sudoroom/magnets/fuck-surveillance/surveillance.dxf

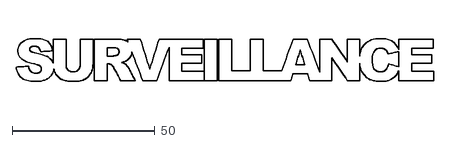
[picture p15: CAD file, 2014-02-05]
fuck-surveillance/surveillance.dxf
146.3 x 15.1
