sudoroom/magnets/hack-the-planet/mesh.stl

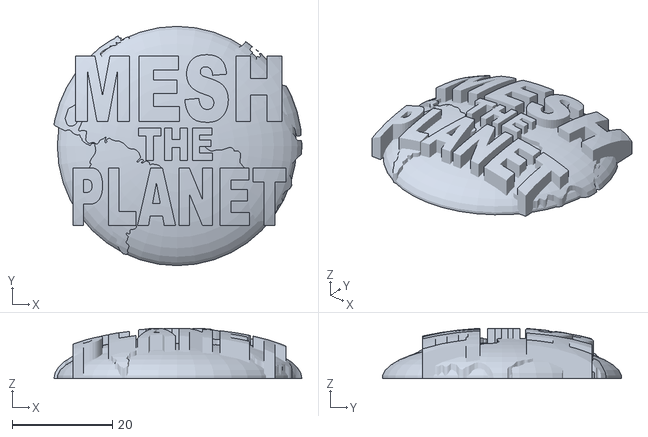
[picture p16: CAD file, 2014-01-22]
hack-the-planet/mesh.stl
49.6 x 47.9 x 10.0
