sudoroom/magnets/sudo/shrunk.dxf

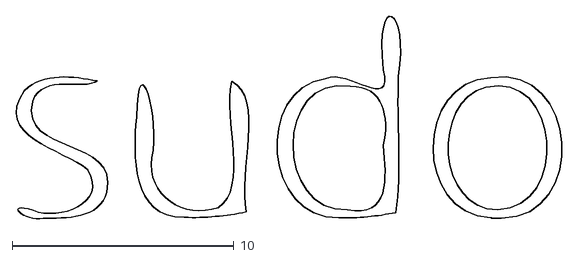
[picture p17: CAD file, 2014-01-15]
sudo/shrunk.dxf
24.6 x 9.11
