sudoroom/magnets/fuck-surveillance/fuck.dxf

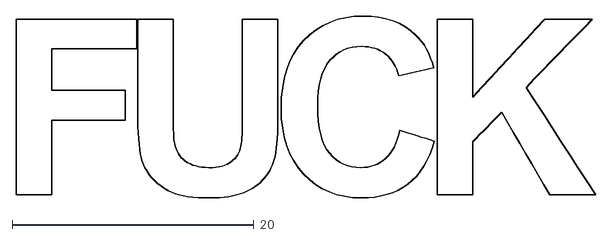
[picture p18: CAD file, 2014-02-05]
fuck-surveillance/fuck.dxf
47.9 x 15.0
