sudoroom/magnets/hack-the-planet/mesh_the_planet.dxf

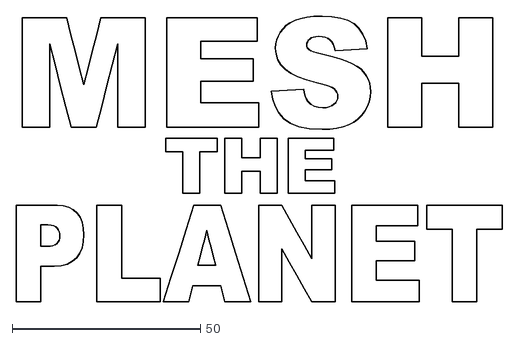
[picture p19: CAD file, 2014-01-13]
hack-the-planet/mesh_the_planet.dxf
129.1 x 75.9
