sudoroom/magnets/fuck-surveillance/no.dxf

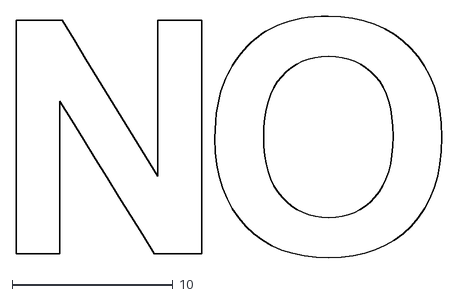
[picture p20: CAD file, 2014-02-05]
fuck-surveillance/no.dxf
26.5 x 15.0
