sudoroom/magnets/hack-the-planet/hack_the_planet.dxf

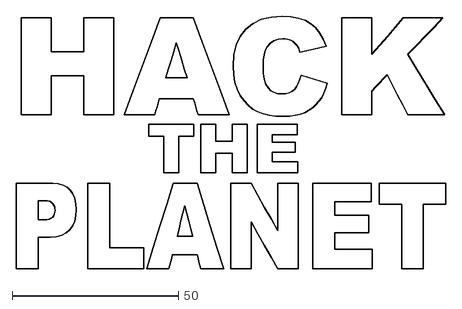
[picture p21: CAD file, 2014-01-12]
hack-the-planet/hack_the_planet.dxf
129.1 x 75.9
