sudoroom/magnets/fuck-surveillance/pictures.dxf

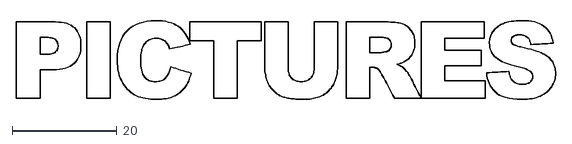
[picture p22: CAD file, 2014-02-05]
fuck-surveillance/pictures.dxf
103.0 x 15.1
