sudoroom/magnets/hack-the-planet/americas.dxf

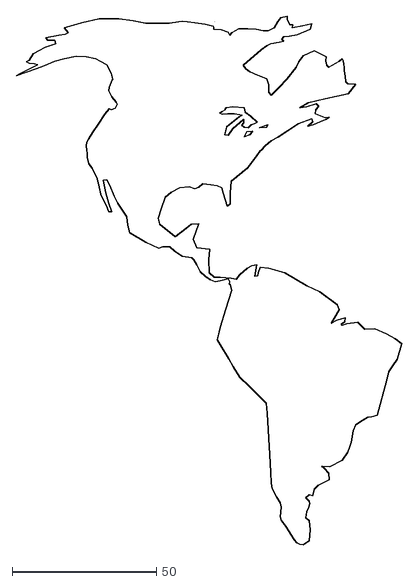
[picture p23: CAD file, 2014-01-11]
hack-the-planet/americas.dxf
133.6 x 183.4
