sudoroom/magnets/hack-the-planet/mesh.scad

difference() {
	union() {
		scale([1,1,0.3]) sphere(r=24,$fn=40);
		intersection() {
			scale([1,1,0.33]) sphere(r=25,$fn=45);
			translate([-35,-24,0])
				scale([0.24,0.24,1])
				linear_extrude(height=9)
				import("world.dxf");
		}
		intersection() {
			scale([1,1,0.35]) sphere(r=29,$fn=50);
			translate([-15,-19,0])
				scale([0.33,0.45,1])
				linear_extrude(height=10)
				import("mesh_the_planet.dxf");
		}
	}
	translate([0,0,0.3])     cylinder(1.75,6.5,6.5);
	translate([0,0,-0.1])    cylinder(1.75,0.5,0.5);
	translate([-50,-50,-50]) cube([100,100,50]);
}
